bogdanbacila/apl-head-tracker/img/assembly/IMG20230302111514.jpg

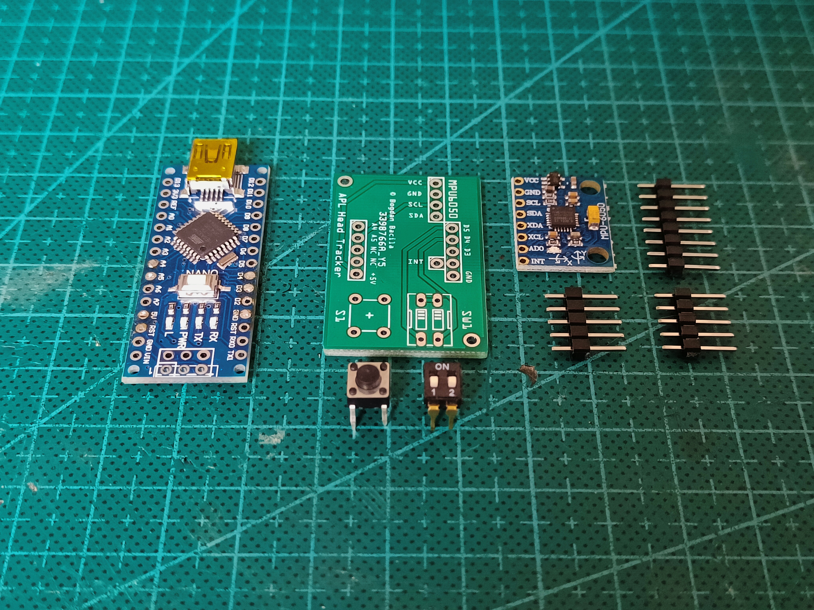
img/assembly/IMG20230302111514.jpg
