bogdanbacila/apl-head-tracker/img/assembly/IMG20230302120007.jpg

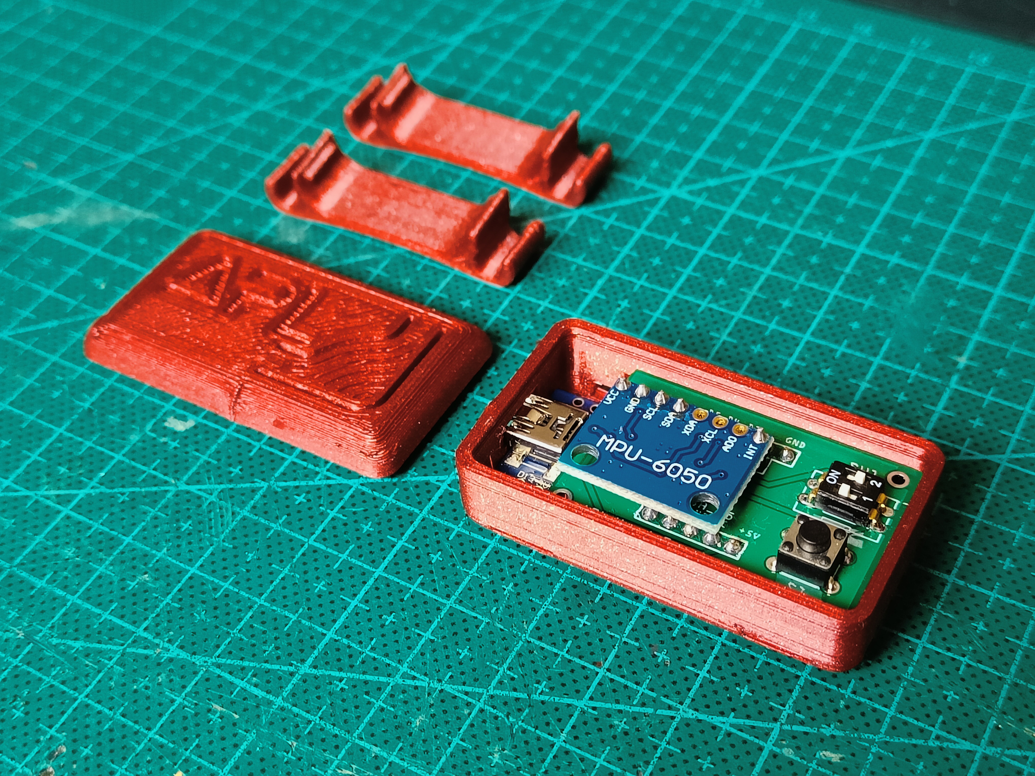
img/assembly/IMG20230302120007.jpg
